itsjonlebron/Backbone-One-iPad-Mini-Upgrade/images/IMG_0007.jpg

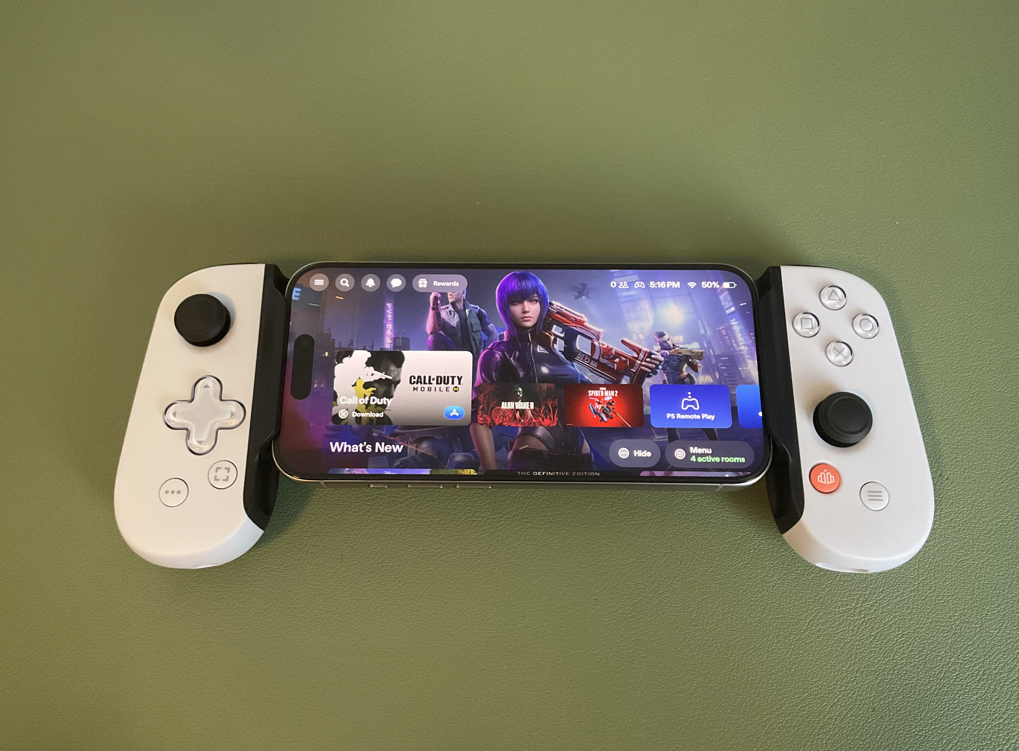
images/IMG_0007.jpg
