itsjonlebron/Backbone-One-iPad-Mini-Upgrade/images/IMG_0008.jpg

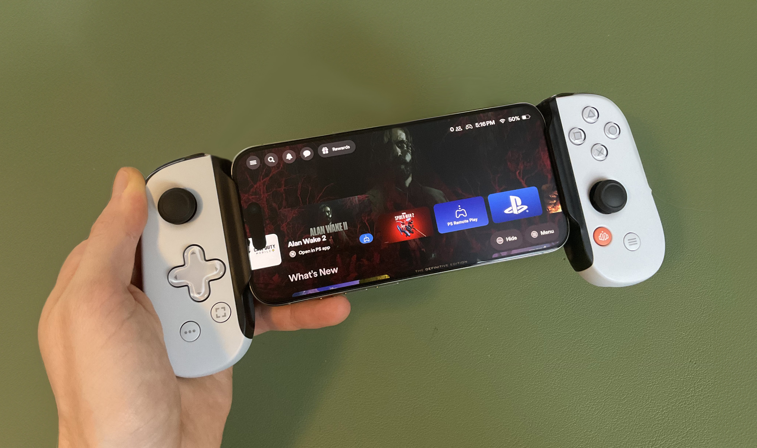
images/IMG_0008.jpg
