itsjonlebron/Backbone-One-iPad-Mini-Upgrade/images/IMG_8249.jpg

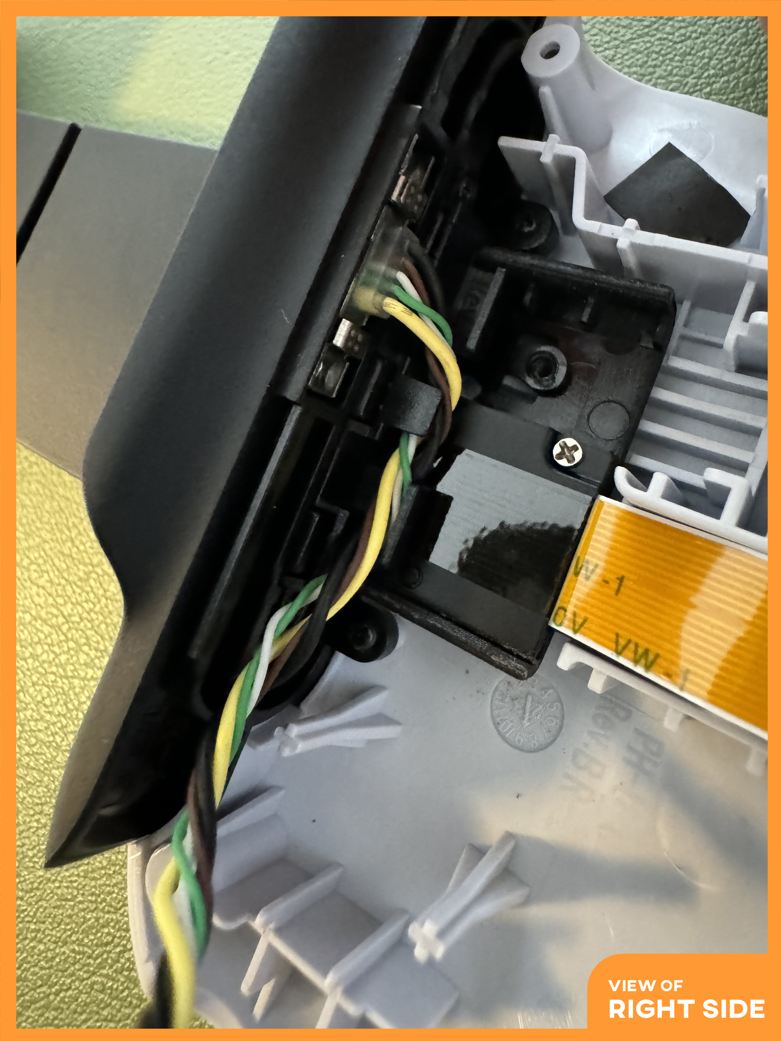
images/IMG_8249.jpg
