itsjonlebron/Backbone-One-iPad-Mini-Upgrade/images/IMG_8262.jpg

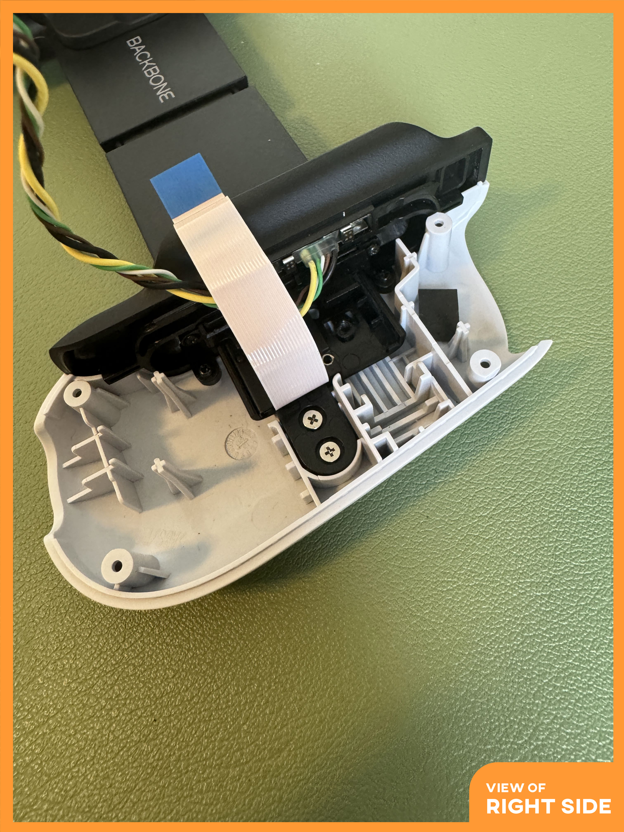
images/IMG_8262.jpg
