itsjonlebron/Backbone-One-iPad-Mini-Upgrade/images/IMG_8264.jpg

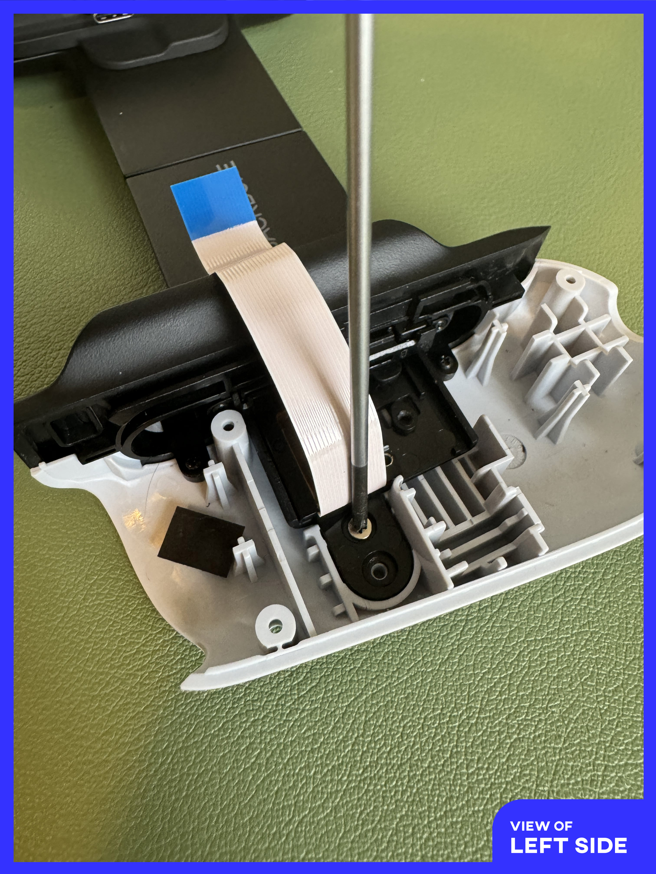
images/IMG_8264.jpg
