itsjonlebron/Backbone-One-iPad-Mini-Upgrade/images/IMG_8266.jpg

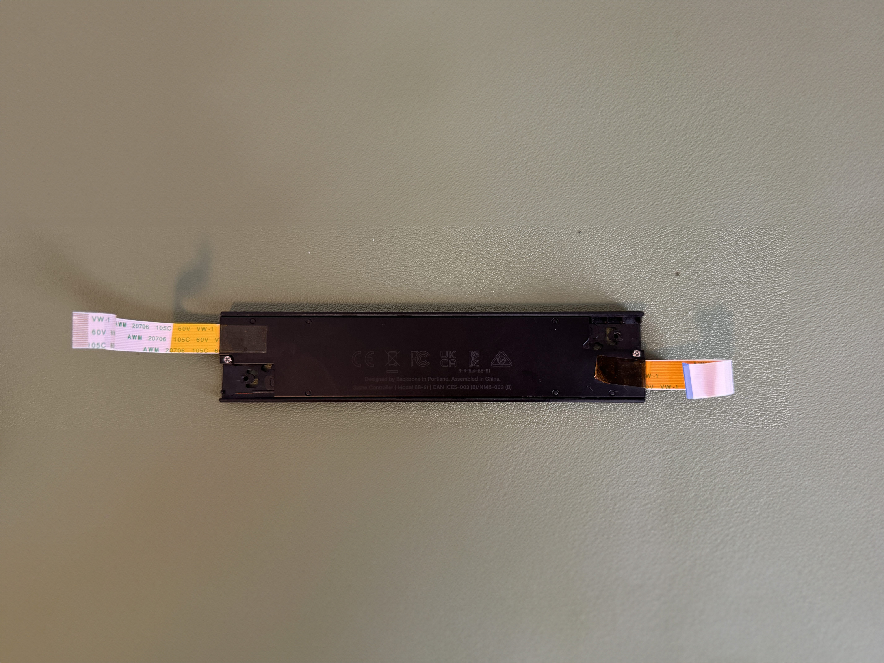
images/IMG_8266.jpg
