itsjonlebron/Backbone-One-iPad-Mini-Upgrade/images/IMG_8268.JPG

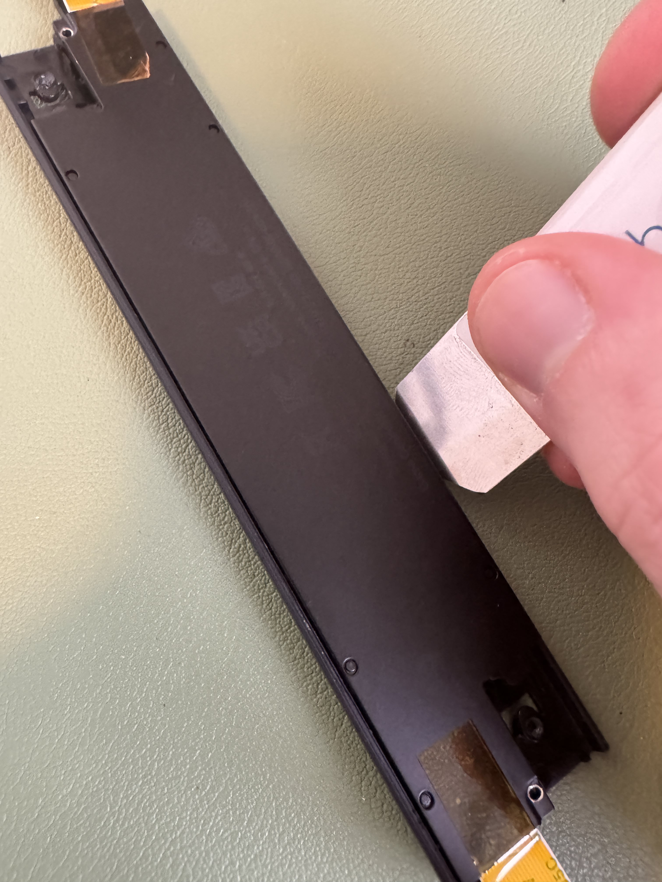
images/IMG_8268.JPG
