itsjonlebron/Backbone-One-iPad-Mini-Upgrade/images/IMG_8283.jpg

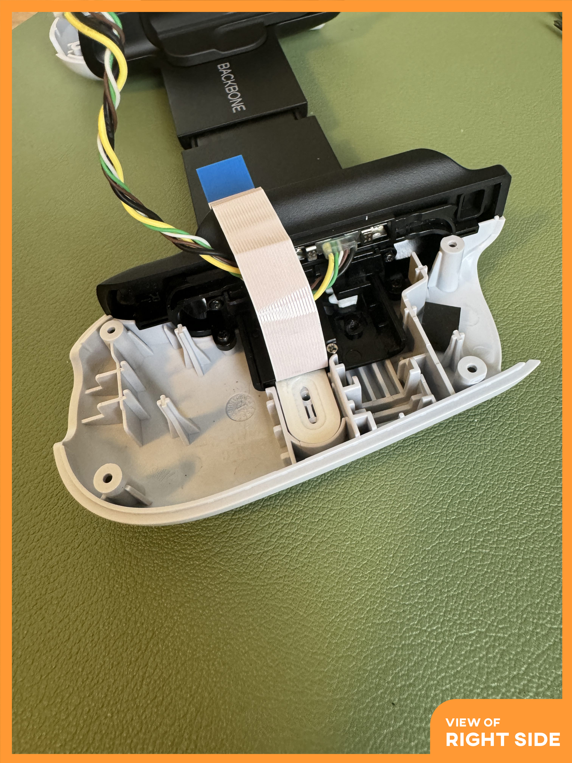
images/IMG_8283.jpg
