itsjonlebron/Backbone-One-iPad-Mini-Upgrade/images/IMG_8287.jpg

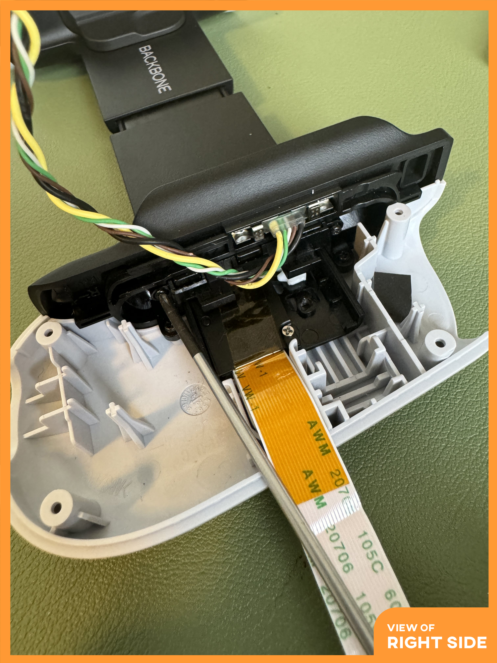
images/IMG_8287.jpg
