itsjonlebron/Backbone-One-iPad-Mini-Upgrade/images/IMG_8288.jpg

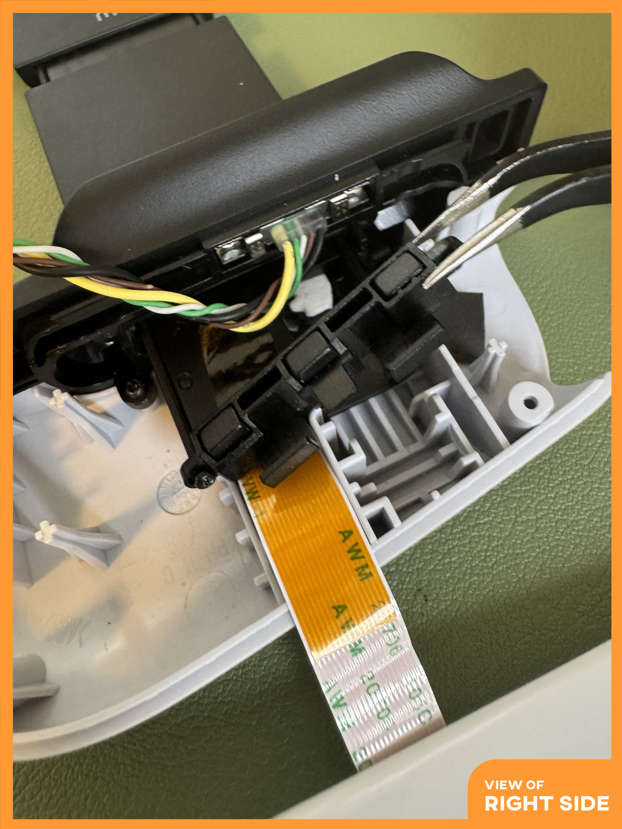
images/IMG_8288.jpg
