itsjonlebron/Backbone-One-iPad-Mini-Upgrade/images/IMG_8289.jpg

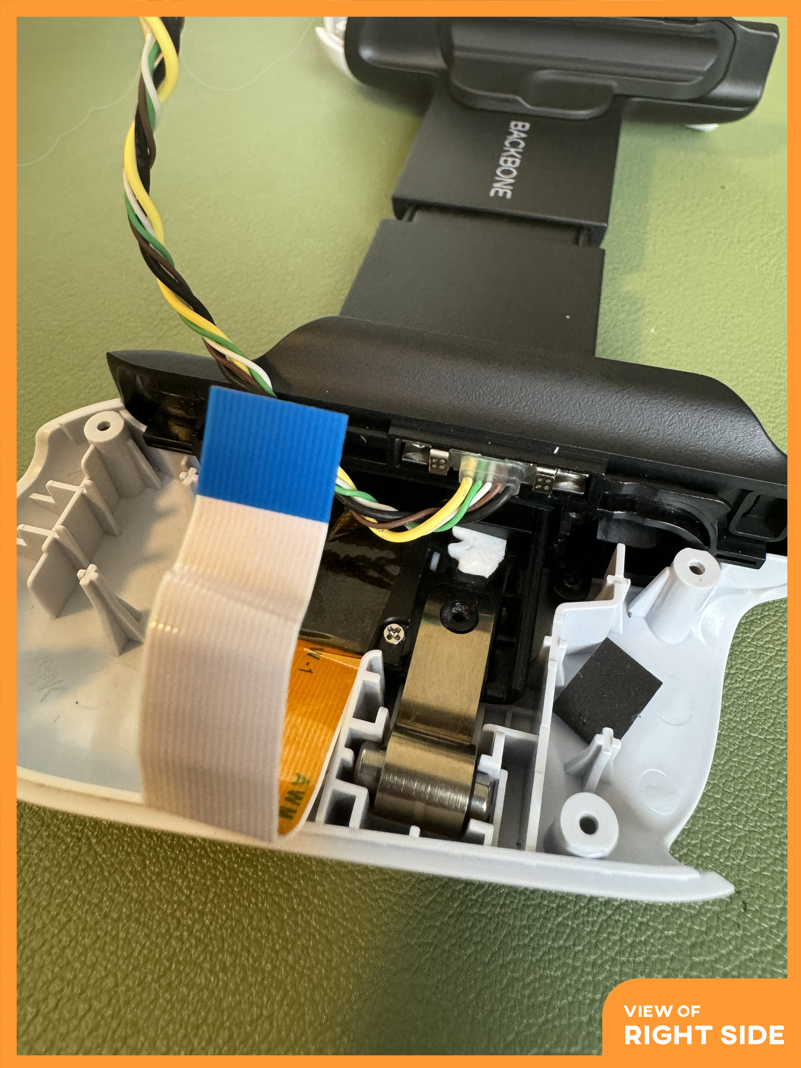
images/IMG_8289.jpg
