itsjonlebron/Backbone-One-iPad-Mini-Upgrade/images/IMG_8296.jpg

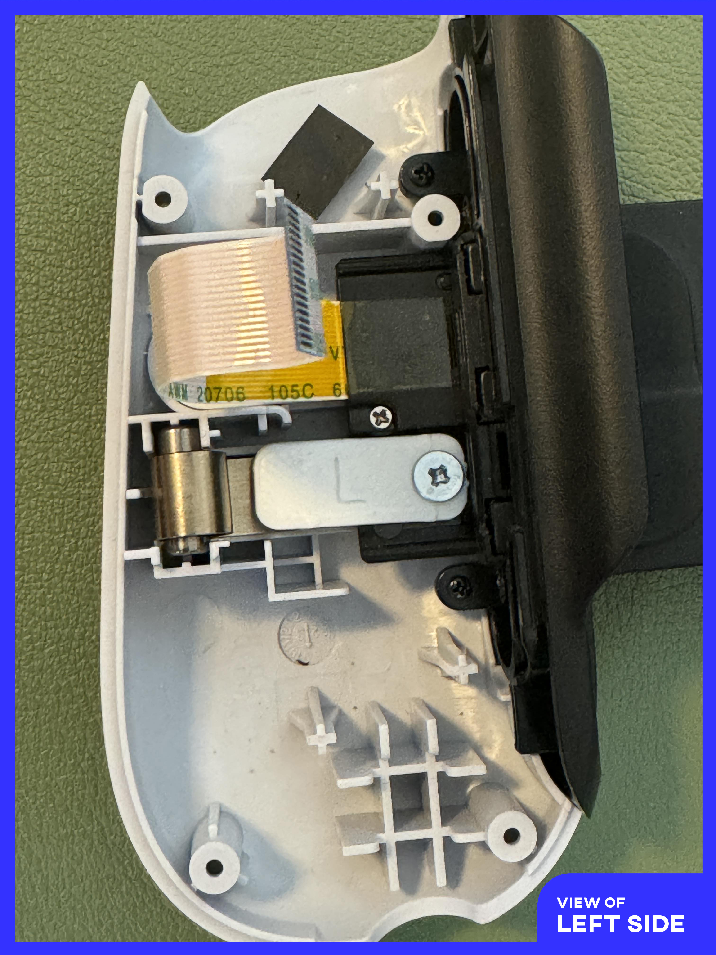
images/IMG_8296.jpg
