itsjonlebron/Backbone-One-iPad-Mini-Upgrade/images/IMG_8300.jpg

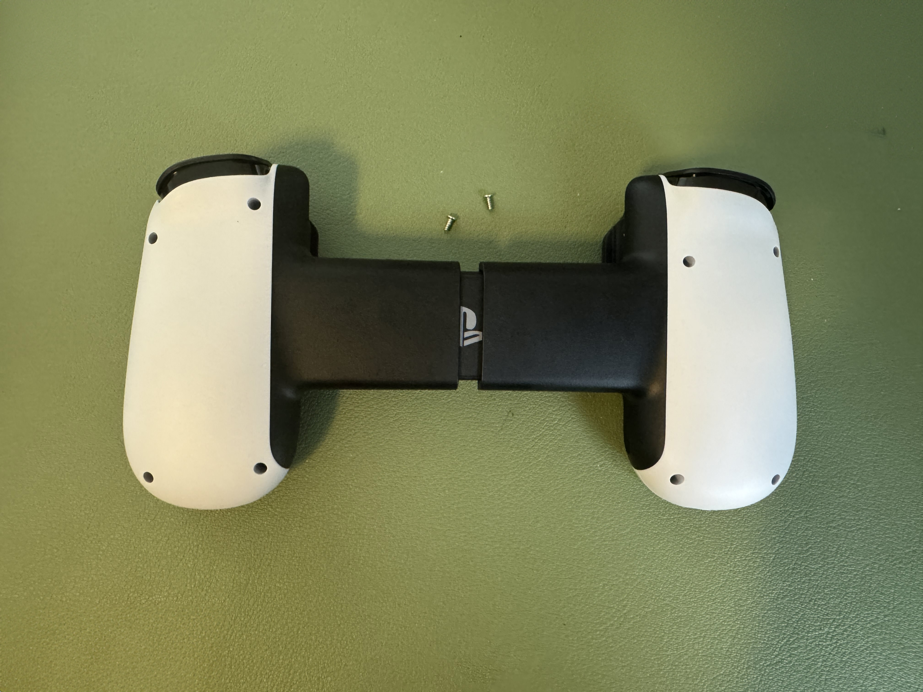
images/IMG_8300.jpg
